PaulKlinger/rps-rnn/rps_rnn_code.X/model_weights.c

#include <stdint.h>
#include "matrix.h"

// unquantized weights from file "deep_3l_s10_softsign_sim.h5"

const uint8_t l1_W_input_data[] = {
         187, 224, 157, 152,   0, 214, 151, 187, 157, 170, 135,  92,  55,
         237, 228,  76, 130, 252, 200,  82, 203, 161, 255, 167, 172, 157,
          22,  51,  88, 162, 161, 162, 150, 178, 148, 161,  98, 153, 123,
         145, 160, 167, 149, 178, 149, 197, 122, 154, 159, 142, 164, 175,
         149, 175, 144,  65, 123, 150, 158, 147};
const struct quantized_matrix l1_W_input = {
    .data = (uint8_t*)l1_W_input_data,
    .rows = 6,
    .cols = 10,
    .scale = 0.03016486822390089,
    .offset = -4.629354
};

const uint8_t l1_W_recurrent_data[] = {
         199,  98, 123,  53, 158, 119, 126, 170, 170, 229, 171, 171, 138,
         149,  85, 133, 148, 113,  96, 126, 209, 174, 213,  91, 200, 166,
         181, 229,  88, 138, 156, 255, 212,  56, 140, 139,  91, 116,  93,
         167,  48, 110, 160, 150, 224,  79, 220, 210,  94, 157, 132, 132,
         138, 134, 142, 126, 133, 147, 128, 146, 144,  85, 133, 119, 146,
         114, 169, 136, 173, 131,  42, 119, 148, 115, 143, 131, 239, 234,
          61, 172, 144, 155, 120, 150, 152, 205, 135, 105,  72, 148, 149,
          96,  63,   0, 176, 125, 174, 146,  99, 104};
const struct quantized_matrix l1_W_recurrent = {
    .data = (uint8_t*)l1_W_recurrent_data,
    .rows = 10,
    .cols = 10,
    .scale = 0.018816572077134077,
    .offset = -2.631897
};

const uint8_t l1_b_state_data[] = {
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
};

const uint8_t l3_b_state_data[] = {
         255, 140, 103, 176, 224,   0,  40, 156, 113, 127};
const struct quantized_matrix l3_b_state = {
    .data = (uint8_t*)l3_b_state_data,
    .rows = 1,
    .cols = 10,
    .scale = 0.008163009905347638,
    .offset = -1.2416106
};

const uint8_t W_output_data[] = {
         157, 160, 145, 255,  13,  87,  71, 112, 233, 155, 149, 194, 250,
           6, 139, 143, 204, 123, 207, 169, 211, 108, 163, 128, 181, 162,
           0, 101, 116, 155};
const struct quantized_matrix W_output = {
    .data = (uint8_t*) W_output_data,
    .rows = 10,
    .cols = 3,
    .scale = 0.012375827864104625,
    .offset = -1.7426877
};

const float b_output_data[] = {
         -0.2723227 , -0.13420135, -0.22269987};
const struct float_matrix b_output = {
    .data = (float*) b_output_data,
    .rows = 1,
    .cols = 3,
};
